barthess/u/hard/pcb/autopilot/IMG_6503.jpg

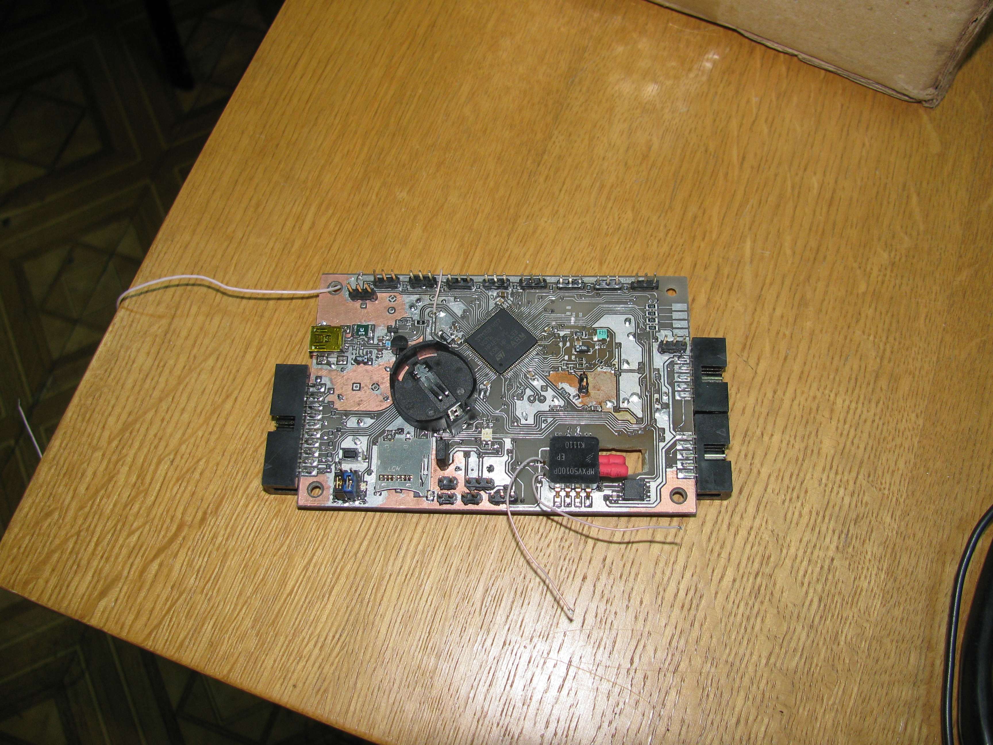
hard/pcb/autopilot/IMG_6503.jpg
