barthess/u/hard/pcb/autopilot/IMG_6504.jpg

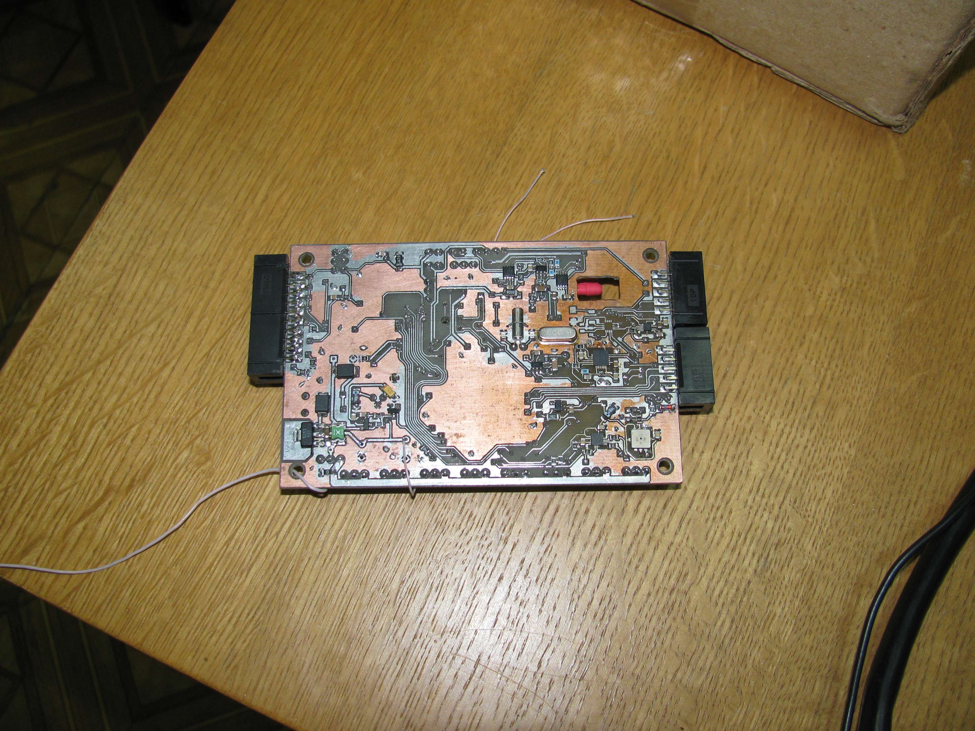
hard/pcb/autopilot/IMG_6504.jpg
