barthess/u/soft/firmware/src/storage/logger_mavencoder.hpp

#ifndef LOGGER_MAVENCODER_H_
#define LOGGER_MAVENCODER_H_

#include "main.h"
#include "message.hpp"

uint16_t mavencoder(uint8_t msg_id, uint8_t system_id, uint8_t *threadsafe_buf, mavlink_message_t* msg);

#endif /* LOGGER_MAVENCODER_H_ */
