barthess/u/soft/firmware/src/acs/acs.cpp

#include <math.h>

#include "main.h"
#include "acs.hpp"
#include "param_registry.hpp"
#include "waypoint_db.hpp"
#include "mission_planner.hpp"
#include "misc_math.hpp"
#include "geometry.hpp"
#include "logger.hpp"
#include "mavdbg.hpp"
#include "sins.hpp"
#include "navigation.hpp"

/*
 ******************************************************************************
 * DEFINES
 ******************************************************************************
 */

/*
 ******************************************************************************
 * EXTERNS
 ******************************************************************************
 */
extern mavlink_system_t                 mavlink_system_struct;
extern mavlink_mission_current_t        mavlink_out_mission_current_struct;
extern mavlink_mission_item_reached_t   mavlink_out_mission_item_reached_struct;
extern mavlink_nav_controller_output_t  mavlink_out_nav_controller_output_struct;
extern mavlink_local_position_ned_t     mavlink_out_local_position_ned_struct;

extern EventSource event_mavlink_out_mission_current;
extern EventSource event_mavlink_out_mission_item_reached;

extern WpDB wpdb;
extern SINS sins;

/*
 ******************************************************************************
 * PROTOTYPES
 ******************************************************************************
 */

/*
 ******************************************************************************
 * GLOBAL VARIABLES
 ******************************************************************************
 */

/*
 ******************************************************************************
 ******************************************************************************
 * LOCAL FUNCTIONS
 ******************************************************************************
 ******************************************************************************
 */

/**
 *
 */
void ACS::broadcast_mission_current(uint16_t seq){
  mavlink_out_mission_current_struct.seq = seq;
  chEvtBroadcastFlags(&event_mavlink_out_mission_current,
                                          EVMSK_MAVLINK_OUT_MISSION_CURRENT);
  log_write_schedule(MAVLINK_MSG_ID_MISSION_CURRENT, NULL, 0);
}

/**
 *
 */
void ACS::broadcast_mission_item_reached(uint16_t seq){
  mavlink_out_mission_item_reached_struct.seq = seq;
  chEvtBroadcastFlags(&event_mavlink_out_mission_item_reached,
                                      EVMSK_MAVLINK_OUT_MISSION_ITEM_REACHED);
  log_write_schedule(MAVLINK_MSG_ID_MISSION_ITEM_REACHED, NULL, 0);
}

/**
 *
 */
void ACS::what_to_do_here(void){
  if ((mi.command == MAV_CMD_NAV_LOITER_UNLIM) ||
      (mi.command == MAV_CMD_NAV_LOITER_TURNS) ||
      (mi.command == MAV_CMD_NAV_LOITER_TIME)){
    /* we must loter here according to mission plan */
    mavlink_dbg_print(MAV_SEVERITY_INFO, "ACS: start loitering");
    loiter_halfturns = 0;
    loiter_timestamp = chTimeNow();
    state = ACS_STATE_LOITER;
  }
  else if(mi.command == MAV_CMD_NAV_WAYPOINT){
    /* this is regular waypoint. Just go to next item */
    state = ACS_STATE_LOAD_MISSION_ITEM;
  }
  else if(mi.command == MAV_CMD_NAV_TAKEOFF){
    /* rover successfully navigated to takeoff point. Go to next item */
    state = ACS_STATE_LOAD_MISSION_ITEM;
  }
  else if(mi.command == MAV_CMD_NAV_LAND){
    /* landing point reached. Go to idle state */
    state = ACS_STATE_IDLE;
    mavlink_system_struct.mode &= ~MAV_MODE_FLAG_SAFETY_ARMED;
    mavlink_system_struct.state = MAV_STATE_STANDBY;
    mavlink_dbg_print(MAV_SEVERITY_INFO, "ACS: Landed");
  }
  else{
    /* do not know hot to handle it. Just got to next */
    state = ACS_STATE_LOAD_MISSION_ITEM;
  }
}

/**
 *
 */
acs_status_t ACS::loop_load_mission_item(void){
  bool load_status = CH_FAILED;

  mi_prev = mi;
  if (wpdb.getCount() <= (mi.seq + 1)){ // no more items
    /* if we fall here than last mission was not 'land'. System do not know
     * what to do so start unlimited loitering */
    state = ACS_STATE_LOITER;
    return ACS_STATUS_NO_MISSION;
  }
  else{
    load_status = wpdb.load(&mi, mi_prev.seq + 1);
    if (CH_SUCCESS != load_status){
      /* something goes wrong with waypoint loading */
      state = ACS_STATE_LOITER;
      return ACS_STATUS_ERROR;
    }
    else{
      broadcast_mission_current(mi.seq);
      sphere.updatePoints(deg2rad(mi_prev.x), deg2rad(mi_prev.y),
                          deg2rad(mi.x),      deg2rad(mi.y));
      state = ACS_STATE_NAVIGATE_TO_WAYPOINT;
      return ACS_STATUS_OK;
    }
  }
}

/*
 ******************************************************************************
 * EXPORTED FUNCTIONS
 ******************************************************************************
 */

ACS::ACS(const StateVector *in, Impact *out){
  this->in = in;
  this->out = out;

  mavlink_out_nav_controller_output_struct.nav_roll       = 0;
  mavlink_out_nav_controller_output_struct.nav_pitch      = 0;
  mavlink_out_nav_controller_output_struct.alt_error      = 0;
  mavlink_out_nav_controller_output_struct.aspd_error     = 0;
  mavlink_out_nav_controller_output_struct.wp_dist        = 0;
  mavlink_out_nav_controller_output_struct.nav_bearing    = 0;
  mavlink_out_nav_controller_output_struct.target_bearing = 0;
  mavlink_out_nav_controller_output_struct.xtrack_error   = 0;

  mavlink_out_local_position_ned_struct.x  = 0;
  mavlink_out_local_position_ned_struct.y  = 0;
  mavlink_out_local_position_ned_struct.z  = 0;
  mavlink_out_local_position_ned_struct.vx = 0;
  mavlink_out_local_position_ned_struct.vy = 0;
  mavlink_out_local_position_ned_struct.vz = 0;
  mavlink_out_local_position_ned_struct.time_boot_ms = TIME_BOOT_MS;

  state = ACS_STATE_UNINIT;
}

/**
 *
 */
acs_status_t ACS::update(void){
  chDbgCheck(ACS_STATE_UNINIT != this->state, "invalid state");
  chDbgCheck((NULL != in) && (NULL != out), "");

  switch(this->state){
  case ACS_STATE_NAVIGATE_TO_WAYPOINT:
    return loop_navigate();
    break;

  case ACS_STATE_LOITER:
    return loop_loiter();
    break;

  case ACS_STATE_PASS_WAYPOINT:
    return loop_passwp();
    break;

  case ACS_STATE_TAKEOFF:
    return loop_takeoff();
    break;

  case ACS_STATE_LOAD_MISSION_ITEM:
    return loop_load_mission_item();
    break;

  case ACS_STATE_LAND:
    return loop_land();
    break;

  case ACS_STATE_PAUSE:
    return loop_pause();
    break;

  case ACS_STATE_IDLE:
    return loop_idle();
    break;

  default:
    chDbgPanic("unhandled case");
    return ACS_STATUS_ERROR;
    break;
  }

  /* warning supressor */
  return ACS_STATUS_ERROR;
}

/**
 * @brief   Launch UAV
 */
MAV_RESULT ACS::takeoff(void){
  chDbgCheck(ACS_STATE_UNINIT != this->state, "invalid state");

  /* check system state */
  if (MAV_STATE_STANDBY != mavlink_system_struct.state){
    mavlink_dbg_print(MAV_SEVERITY_ERROR, "ERROR: system must be in STANDBY");
    return MAV_RESULT_TEMPORARILY_REJECTED;
  }

  /* system disarmed */
  if (!(mavlink_system_struct.mode & MAV_MODE_FLAG_SAFETY_ARMED)){
    mavlink_dbg_print(MAV_SEVERITY_ERROR, "ERROR: motors disarmed");
    return MAV_RESULT_TEMPORARILY_REJECTED;
  }

  /* allready done */
  if (ACS_STATE_IDLE != state){
    mavlink_dbg_print(MAV_SEVERITY_ERROR, "ERROR: mission in process");
    return MAV_RESULT_TEMPORARILY_REJECTED;
  }

  /* try to load start of mission to RAM */
  if (0 == wpdb.getCount()){
    mavlink_dbg_print(MAV_SEVERITY_ERROR, "ERROR: mission empty");
    return MAV_RESULT_TEMPORARILY_REJECTED;
  }
  if (CH_SUCCESS != wpdb.load(&mi, 0))
    chDbgPanic("can not acquare waypoint");
  if (mi.command != MAV_CMD_NAV_TAKEOFF)
    chDbgPanic("first item must be takeoff");

  switch(mi.frame){
  /*
   * local frame handler
   */
  case MAV_FRAME_LOCAL_NED:
    mi_prev = mi; // hack to fill all other fields correctly
    mi_prev.x = 0;
    mi_prev.y = 0;
    mi_prev.z = 0;
    launch_lat = 0;
    launch_lon = 0;
    launch_alt = 0;
    break;

  /*
   * global fram handler
   */
  case MAV_FRAME_GLOBAL:
    if (in->gpsfix < 2){    /* can not fly without GPS */
      mavlink_dbg_print(MAV_SEVERITY_ERROR, "ERROR: no GPS fix");
      return MAV_RESULT_TEMPORARILY_REJECTED;
    }
    else{
      launch_lon = in->lon;
      launch_lat = in->lat;
      launch_alt = in->hmsl;
      sphere.updatePoints(launch_lat, launch_lon, deg2rad(mi.x), deg2rad(mi.y));
      mi_prev = mi; // hack to fill all other fields correctly
      mi_prev.x = launch_lat;
      mi_prev.y = launch_lon;
      mi_prev.z = launch_alt;
    }
    break;

  /*
   * error trap
   */
  default:
    chDbgPanic("unhandled case");
    break;
  }

  sins.reset();
  mavlink_dbg_print(MAV_SEVERITY_INFO, "ACS: Taking off");
  state = ACS_STATE_TAKEOFF;
  mavlink_system_struct.state = MAV_STATE_ACTIVE;
  broadcast_mission_current(mi.seq);
  return MAV_RESULT_ACCEPTED;
}

/**
 * Set specified waypoint as current and go to it
 */
MAV_RESULT ACS::jump_to(uint16_t seq){
  bool load_status = CH_FAILED;

  /* check current state of ACS */
  if (! ((ACS_STATE_LOAD_MISSION_ITEM == state) ||
      (ACS_STATE_NAVIGATE_TO_WAYPOINT == state) ||
             (ACS_STATE_PASS_WAYPOINT == state) ||
                    (ACS_STATE_LOITER == state) ||
                     (ACS_STATE_PAUSE == state))){
    mavlink_dbg_print(MAV_SEVERITY_ERROR, "ERROR: Can not jump in this state");
    return MAV_RESULT_TEMPORARILY_REJECTED;
  }

  // set current location as previouse point
  mi_prev.x = in->lat;
  mi_prev.y = in->lon;
  mi_prev.z = in->hmsl;

  // load last waypoint
  load_status = wpdb.load(&mi, seq);
  if (CH_SUCCESS != load_status){
    /* something goes wrong with waypoint loading */
    state = ACS_STATE_LOITER;
    return MAV_RESULT_FAILED;
  }
  else{
    broadcast_mission_current(mi.seq);
    sphere.updatePoints(deg2rad(mi_prev.x), deg2rad(mi_prev.y),
                        deg2rad(mi.x),      deg2rad(mi.y));
    state = ACS_STATE_NAVIGATE_TO_WAYPOINT;
    return MAV_RESULT_ACCEPTED;
  }
}





/**
 * Set last waypoint as current and go to it
 */
MAV_RESULT ACS::emergencyGotoLand(mavlink_command_long_t *clp){
  (void)clp;
  //return jump_to(wpdb.getCount() - 1);

  // HACK: to emergency stop uas
  state = ACS_STATE_IDLE;
  mavlink_system_struct.mode &= ~MAV_MODE_FLAG_SAFETY_ARMED;
  mavlink_system_struct.state = MAV_STATE_STANDBY;
  mavlink_dbg_print(MAV_SEVERITY_INFO, "ACS: Landed");

  return MAV_RESULT_ACCEPTED;
}







/**
 * @brief   Used for emergency pause the mission.
 */
MAV_RESULT ACS::overrideGoto(mavlink_command_long_t *clp){
  /* Hold / continue the current action
   * | MAV_GOTO_DO_HOLD: hold
   *   MAV_GOTO_DO_CONTINUE: continue with next item in mission plan
   *
   * | MAV_GOTO_HOLD_AT_CURRENT_POSITION: Hold at current position
   *   MAV_GOTO_HOLD_AT_SPECIFIED_POSITION: hold at specified position
   *
   * | MAV_FRAME coordinate frame of hold point
   * | Desired yaw angle in degrees
   * | Latitude / X position
   * | Longitude / Y position
   * | Altitude / Z position|  */

  /* pause at current position */
  if (clp->param1 == MAV_GOTO_DO_HOLD &&
      clp->param2 == MAV_GOTO_HOLD_AT_CURRENT_POSITION &&
      clp->param3 == 0 &&
      clp->param4 == 0 &&
      clp->param5 == 0 &&
      clp->param6 == 0 &&
      clp->param7 == 0){

    if (ACS_STATE_NAVIGATE_TO_WAYPOINT != state){
      mavlink_dbg_print(MAV_SEVERITY_ERROR, "ERROR: pause allowed only during navigation");
      return MAV_RESULT_TEMPORARILY_REJECTED;
    }
    else{
      state = ACS_STATE_PAUSE;
      mavlink_dbg_print(MAV_SEVERITY_INFO, "INFO: mission paused");
      return MAV_RESULT_ACCEPTED;
    }
  }

  /* unpause */
  else if (clp->param1 == MAV_GOTO_DO_CONTINUE &&
           clp->param2 == MAV_GOTO_HOLD_AT_CURRENT_POSITION &&
           clp->param3 == 0 &&
           clp->param4 == 0 &&
           clp->param5 == 0 &&
           clp->param6 == 0 &&
           clp->param7 == 0){

    if (ACS_STATE_PAUSE != state){
      mavlink_dbg_print(MAV_SEVERITY_ERROR, "ERROR: continue allowed only during pause");
      return MAV_RESULT_TEMPORARILY_REJECTED;
    }
    else{
      state = ACS_STATE_NAVIGATE_TO_WAYPOINT;
      mavlink_dbg_print(MAV_SEVERITY_INFO, "INFO: mission continued");
      return MAV_RESULT_ACCEPTED;
    }
  }

  /* unrealized */
  else{
    return MAV_RESULT_UNSUPPORTED;
  }
}

/**
 *
 */
MAV_RESULT ACS::returnToLaunch(mavlink_command_long_t *clp){
  (void)clp;
  return jump_to(0);
}

/**
 *
 */
MAV_RESULT ACS::setCurrentMission(mavlink_mission_set_current_t *sc){
  chDbgCheck(ACS_STATE_UNINIT != this->state, "invalid state");
  return jump_to(sc->seq);
}

/**
 * Set autopilot mode logic.
 */
void ACS::setMode(mavlink_set_mode_t *sm){
  /* safety armed bit can be changed only in STANDBY mode*/
  if ((mavlink_system_struct.mode & MAV_MODE_FLAG_SAFETY_ARMED) !=
                   (sm->base_mode & MAV_MODE_FLAG_SAFETY_ARMED)){
    if (! (MAV_STATE_STANDBY == mavlink_system_struct.state &&
           ACS_STATE_IDLE == state)){
      mavlink_dbg_print(MAV_SEVERITY_ERROR, "ERROR: system must be in STANDBY");
      return;
    }
  }

  /* mode can be changed */
  mavlink_system_struct.mode = sm->custom_mode | sm->base_mode;
}

/**
 *
 */
void ACS::manualControl(mavlink_manual_control_t *mc){
  chDbgCheck(ACS_STATE_UNINIT != this->state, "invalid state");

  uint32_t v = 0;
  (void)v;
  (void)mc;
  mavlink_dbg_print(MAV_SEVERITY_ERROR, "ERROR: manual control unrealized");
//  if (mc->thrust_manual == 1){
//    v = float2thrust(mc->thrust);
//    ServoCarThrustSet(v);
//  }
//  if (mc->yaw_manual == 1){
//    v = float2servo(mc->yaw);
//    Servo7Set(v);
//  }
}
