barthess/u/soft/firmware/src/sanity.cpp

#include "main.h"
#include "global_flags.h"
#include "fault_handlers.h"

#include "message.hpp"
#include "timekeeping.hpp"
#include "bkp.hpp"
#include "logger.hpp"

/*
 ******************************************************************************
 * EXTERNS
 ******************************************************************************
 */
extern GlobalFlags_t GlobalFlags;
extern uint32_t LastResetFlags;

extern mavlink_system_t       mavlink_system_struct;
extern mavlink_heartbeat_t    mavlink_out_heartbeat_struct;
extern mavlink_sys_status_t   mavlink_out_sys_status_struct;

extern EventSource event_mavlink_out_heartbeat;
extern chibios_rt::Mailbox blue_blink_mb;

/*
 ******************************************************************************
 * DEFINES
 ******************************************************************************
 */
#define HEART_BEAT_PERIOD   MS2ST(1000)

/* how much time led is ON during flash */
#define BLUE_LED_ON_TIME    MS2ST(50)
#define BLUE_LED_OFF_TIME   MS2ST(100)

#define SYS_STATUS_3D_GYRO    ((uint32_t)1 << 0) /* for stub */
#define SYS_STATUS_3D_ACCEL   ((uint32_t)1 << 1) /* for stub */
#define SYS_STATUS_3D_MAG     ((uint32_t)1 << 2) /* for stub */
#define SYS_STATUS_ABS_PRES   ((uint32_t)1 << 3) /* for stub */
#define SYS_STATUS_DIFF_PRES  ((uint32_t)1 << 4) /* for stub */
#define SYS_STATUS_GPS        ((uint32_t)1 << 5) /* for stub */

/*
 ******************************************************************************
 * GLOBAL VARIABLES
 ******************************************************************************
 */
static const int16_t normal[]      = {50,  -100, 0};
static const int16_t panic[]       = {50,  -100, 50, -100, 50, -100, 50, -100, 0};
static const int16_t calibrating[] = {800, -200, 0};

/*
 *******************************************************************************
 *******************************************************************************
 * LOCAL FUNCTIONS
 *******************************************************************************
 *******************************************************************************
 */

/**
 * Heartbeat blinker logic
 */
static void heartbeat_blinker(void){
  if (was_softreset()){
    blue_blink_mb.post((msg_t)panic, TIME_IMMEDIATE);
  }
  else{
    if (MAV_STATE_CALIBRATING == mavlink_system_struct.state)
      blue_blink_mb.post((msg_t)calibrating, TIME_IMMEDIATE);
    else
      blue_blink_mb.post((msg_t)normal, TIME_IMMEDIATE);
  }
}

/**
 * посылает heartbeat пакеты и моргает светодиодиком
 */
static WORKING_AREA(SanityControlThreadWA, 128);
static msg_t SanityControlThread(void *arg) {
  chRegSetThreadName("Sanity");
  (void)arg;

  mavlink_out_heartbeat_struct.autopilot = MAV_AUTOPILOT_GENERIC;
  mavlink_out_heartbeat_struct.custom_mode = 0;

  systime_t t = chTimeNow();

  while (TRUE) {
    t += HEART_BEAT_PERIOD;

    /* fill data fields */
    if (GlobalFlags.tlm_link_ready){
      mavlink_out_heartbeat_struct.type           = mavlink_system_struct.type;
      mavlink_out_heartbeat_struct.base_mode      = mavlink_system_struct.mode;
      mavlink_out_heartbeat_struct.system_status  = mavlink_system_struct.state;
      chEvtBroadcastFlags(&event_mavlink_out_heartbeat, EVMSK_MAVLINK_OUT_HEARTBEAT);

      /* stub */
      mavlink_out_sys_status_struct.onboard_control_sensors_present = (
              SYS_STATUS_3D_GYRO | SYS_STATUS_3D_ACCEL | SYS_STATUS_3D_MAG |
              SYS_STATUS_ABS_PRES | SYS_STATUS_DIFF_PRES | SYS_STATUS_GPS);
      mavlink_out_sys_status_struct.onboard_control_sensors_enabled = mavlink_out_sys_status_struct.onboard_control_sensors_present;
      mavlink_out_sys_status_struct.onboard_control_sensors_health  = mavlink_out_sys_status_struct.onboard_control_sensors_present;
    }

    log_write_schedule(MAVLINK_MSG_ID_HEARTBEAT, NULL, 0);

    mavlink_out_sys_status_struct.load = getCpuLoad();
    /* how many times device was soft resetted */
    mavlink_out_sys_status_struct.errors_count1 = bkpSoftResetCnt;
    /* reset flags */
    mavlink_out_sys_status_struct.errors_count2 = LastResetFlags >> 24;
    if (GlobalFlags.sighalt){
      palClearPad(GPIOB, GPIOB_LED_B);
      palClearPad(GPIOB, GPIOB_LED_R);
      xbee_reset_assert();
      chThdExit(RDY_OK);
    }

    heartbeat_blinker();
    chThdSleepUntil(t);
  }
  return 0;
}

/*
 *******************************************************************************
 * EXPORTED FUNCTIONS
 *******************************************************************************
 */
/**
 *
 */
void SanityControlInit(void){

  chDbgCheck(1 == GlobalFlags.blinker_ready, "blinker not ready");

  /* write soft reset event to "log" and clean it in case of pad reset */
  if (was_softreset())
    bkpSoftResetCnt++;

  /**/
  chThdCreateStatic(SanityControlThreadWA,
          sizeof(SanityControlThreadWA),
          NORMALPRIO,
          SanityControlThread,
          NULL);
}
