barthess/u/soft/firmware/src/storage/logger.cpp

#include <string.h>

#include "main.h"
#include "global_flags.h"
#include "ff.h"
#include "message.hpp"
#include "logger_mavencoder.hpp"

/*
 ******************************************************************************
 * DEFINES
 ******************************************************************************
 */

/* FS buffer size */
#define BUFF_SIZE 8192

/* how many spare bytes we have in buffer */
#define FREE (BUFF_SIZE - offset)

/* length of timestamp field in mavlink log record */
#if MAVLINK_LOG_FORMAT
#define TIME_LEN    (sizeof(uint64_t))
#else
#define TIME_LEN    0
#endif

/* length of record */
#define RECORD_LEN  (MAVLINK_MAX_PACKET_LEN + TIME_LEN)

/*
 ******************************************************************************
 * EXTERNS
 ******************************************************************************
 */
extern GlobalFlags_t GlobalFlags;
extern chibios_rt::Mailbox logwriter_mb;
extern mavlink_system_t mavlink_system_struct;

/*
 ******************************************************************************
 * GLOBAL VARIABLES
 ******************************************************************************
 */

/* 2 switching buffers */
static uint8_t b0[BUFF_SIZE];
static uint8_t b1[BUFF_SIZE];

/* pointer to current working buffer */
static uint8_t* CurrentBuffer = b0;

/* offset in current buffer */
static uint32_t offset = 0;

/*
 ******************************************************************************
 * PROTOTYPES
 ******************************************************************************
 */

/*
 *******************************************************************************
 *******************************************************************************
 * LOCAL FUNCTIONS
 *******************************************************************************
 *******************************************************************************
 */

/**
 * Switch pointer to next free buffer.
 */
static void swap_buf(void){
  if (CurrentBuffer == b0)
    CurrentBuffer = b1;
  else
    CurrentBuffer = b0;
}


/**
 * Fit data to double buffer.
 * return pointer to full buffer or NULL if current buffer is not full
 */
static uint8_t* bufferize(uint8_t *payload, uint32_t count){

  uint8_t *ret;

  if (FREE > count){
    memcpy(CurrentBuffer + offset, payload, count);
    offset += count;
    return NULL;
  }
  else{
    /* put in current buffer as much as possible */
    memcpy(CurrentBuffer + offset, payload, FREE);
    /* this pointer will be returned as a result of work */
    ret = CurrentBuffer;
    /* switch to free buffer */
    swap_buf();
    /* rest of data put in free buffer */
    memcpy(CurrentBuffer, payload + FREE, count - FREE);
    offset = count - FREE;
    return ret;
  }
}

/*
 *******************************************************************************
 * EXPORTED FUNCTIONS
 *******************************************************************************
 */

/**
 * Get id of data
 * Pack it
 * Store to FS buffer
 * Raise bool flag if fresh data available
 */
FRESULT WriteLog(FIL *Log, msg_t id, bool_t *fresh_data){
  uint32_t bytes_written;
  uint8_t *fs_buf;
  FRESULT err = FR_OK;

  /* some buffers for mavlink handling */
  mavlink_message_t mavlink_msgbuf_log;
  uint8_t recordbuf[RECORD_LEN];

  mavencoder(id, mavlink_system_struct.sysid, recordbuf, &mavlink_msgbuf_log);

#if MAVLINK_LOG_FORMAT
#if CH_DBG_ENABLE_CHECKS
  /* fill buffer with zeros except the timestamp region. Probably not necessary */
  memset(recordbuf + TIME_LEN, 0, RECORD_LEN - TIME_LEN);
#endif
  uint64_t timestamp = pnsGetTimeUnixUsec();
  mavlink_msg_to_send_buffer(recordbuf + TIME_LEN, &mavlink_msgbuf_log);
  memcpy(recordbuf, &timestamp, TIME_LEN);
  fs_buf = bufferize(recordbuf, RECORD_LEN);
#else /* MAVLINK_LOG_FORMAT */
  uint16_t len = 0;
  len = mavlink_msg_to_send_buffer(recordbuf, &mavlink_msgbuf_log);
  fs_buf = bufferize(recordbuf, len);
#endif /* MAVLINK_LOG_FORMAT */

  if (fs_buf != NULL){
    err = f_write(Log, fs_buf, BUFF_SIZE, (UINT *)&bytes_written);
    if (err == FR_OK)
      *fresh_data = TRUE;
  }
  return err;
}

/**
 *
 * @brief   Macro helper. Shedule writing specified message to log.
 *
 * @param[in] id      Mavlink message id.
 * @param[in] *i      External counter. Set to NULL if you do not need "traffic shaping"
 * @param[in] decimator Variable to regulate writing frequency.
 * @api
 */
void log_write_schedule(uint8_t id, uint32_t *i, uint32_t decimator) {
  if (GlobalFlags.logger_ready){
    if (i == NULL){
      logwriter_mb.post(id, TIME_IMMEDIATE);
      return;
    }
    else if ((*i & decimator) == decimator){
      logwriter_mb.post(id, TIME_IMMEDIATE);
    }
    (*i)++;
  }
}
