barthess/u/soft/firmware/src/imu.c

#include <math.h>

#include "ch.h"
#include "hal.h"

#include "message.h"
#include "main.h"
#include "imu.h"
#include "link.h"
#include "param.h"
#include "itg3200.h"

/*
 ******************************************************************************
 * DEFINES
 ******************************************************************************
 */
#define GYRO_SENS 14.375f

/*
 ******************************************************************************
 * EXTERNS
 ******************************************************************************
 */
extern Mailbox tolink_mb;
extern uint64_t TimeUsec;
extern mavlink_raw_imu_t mavlink_raw_imu_struct;
extern GlobalParam_t global_data[];
extern RawData raw_data;
extern CompensatedData comp_data;
extern BinarySemaphore imu_sem;

extern uint32_t itg3200_period;

/*
 ******************************************************************************
 * GLOBAL VARIABLES
 ******************************************************************************
 */

/*
 *******************************************************************************
 *******************************************************************************
 * LOCAL FUNCTIONS
 *******************************************************************************
 *******************************************************************************
 */

/**
 * Перевод условных единиц в градусы
 */
static float get_degrees(int32_t raw){
  float s = 1000000.0; /* угол поворота интегрируется по микросекундам */
  return ((float)raw * itg3200_period) / (GYRO_AVG_SAMPLES_CNT * GYRO_SENS * s);
}

/**
 * Поток обработки инерациальных данных
 */
static WORKING_AREA(waImu, 256);
static msg_t Imu(void *arg) {
  (void)arg;
  chRegSetThreadName("IMU");
  msg_t sem_status = RDY_TIMEOUT;

  while (TRUE) {
    sem_status = chBSemWaitTimeout(&imu_sem, MS2ST(100));
    if (sem_status == RDY_OK){
      comp_data.xgyro_f += get_degrees(raw_data.xgyro_delta);
      comp_data.ygyro_f += get_degrees(raw_data.ygyro_delta);
      comp_data.zgyro_f += get_degrees(raw_data.zgyro_delta);
    }
  }
  return 0;
}

/**
 * Посылалка телеметрии
 */
static WORKING_AREA(waImuSender, 256);
static msg_t ImuSender(void *arg) {
  (void)arg;
  chRegSetThreadName("IMU_Sender");

  Mail tolink_mail = {NULL, MAVLINK_MSG_ID_RAW_IMU, NULL};

  uint32_t i = key_value_search("IMU_send_ms");

  while (TRUE) {
    chThdSleepMilliseconds(global_data[i].value);
    if (tolink_mail.payload == NULL){
      mavlink_raw_imu_struct.xgyro      = floorf(comp_data.xgyro_f * 100);
      mavlink_raw_imu_struct.ygyro      = floorf(comp_data.ygyro_f * 100);
      mavlink_raw_imu_struct.zgyro      = floorf(comp_data.zgyro_f * 100);
      mavlink_raw_imu_struct.time_usec  = TimeUsec;

      tolink_mail.payload = &mavlink_raw_imu_struct;
      chMBPost(&tolink_mb, (msg_t)&tolink_mail, TIME_IMMEDIATE);
    }
  }
  return 0;
}

/*
 *******************************************************************************
 * EXPORTED FUNCTIONS
 *******************************************************************************
 */
void ImuInit(void){
  chThdCreateStatic(waImu, sizeof(waImu), NORMALPRIO, Imu, NULL);
  chThdCreateStatic(waImuSender, sizeof(waImuSender), NORMALPRIO, ImuSender, NULL);
}

/**
 * Сбрасывает всё рассчитанное инерциалкой в начальное состояние
 */
void ImuReset(void){

}
