barthess/u/soft/firmware/src/acs/acs_rover_idle.cpp

#include <math.h>

#include "main.h"
#include "acs_rover.hpp"

/*
 ******************************************************************************
 * DEFINES
 ******************************************************************************
 */

/*
 ******************************************************************************
 * EXTERNS
 ******************************************************************************
 */

/*
 ******************************************************************************
 * PROTOTYPES
 ******************************************************************************
 */

/*
 ******************************************************************************
 * GLOBAL VARIABLES
 ******************************************************************************
 */

/*
 ******************************************************************************
 ******************************************************************************
 * LOCAL FUNCTIONS
 ******************************************************************************
 ******************************************************************************
 */

/**
 *
 */
acs_status_t ACSRover::loop_idle(void){
  /* for ground rover we must just to pull handbrake and wait command */
  pull_handbreak();
  return ACS_STATUS_OK;
}
