barthess/u/soft/firmware/src/acs/acs_pause.cpp

#include <math.h>

#include "main.h"
#include "acs.hpp"

/*
 ******************************************************************************
 * DEFINES
 ******************************************************************************
 */

/*
 ******************************************************************************
 * EXTERNS
 ******************************************************************************
 */

/*
 ******************************************************************************
 * PROTOTYPES
 ******************************************************************************
 */

/*
 ******************************************************************************
 * GLOBAL VARIABLES
 ******************************************************************************
 */

/*
 ******************************************************************************
 ******************************************************************************
 * LOCAL FUNCTIONS
 ******************************************************************************
 ******************************************************************************
 */

/**
 *
 */
acs_status_t ACS::loop_pause(void){
  /* for ground rover we must just to pull handbrake and wait next command */
  pull_handbreak();
  return ACS_STATUS_OK;
}
